gmhull/Macro-Pad/boot.py

import board
import storage
import usb_cdc

from digitalio import DigitalInOut, Direction, Pull

row = DigitalInOut(board.D2)
col = DigitalInOut(board.D5)

row.direction = Direction.INPUT
col.direction = Direction.OUTPUT

row.pull = Pull.DOWN
col.value = True

if not row.value:
    storage.disable_usb_drive()
    usb_cdc.disable()
